TianmingLi/jetson-nano-baseboard/USB-3_2-HUB.kicad_sch

## KiCad design USB-3_2-HUB.kicad_sch (2023-06-30)

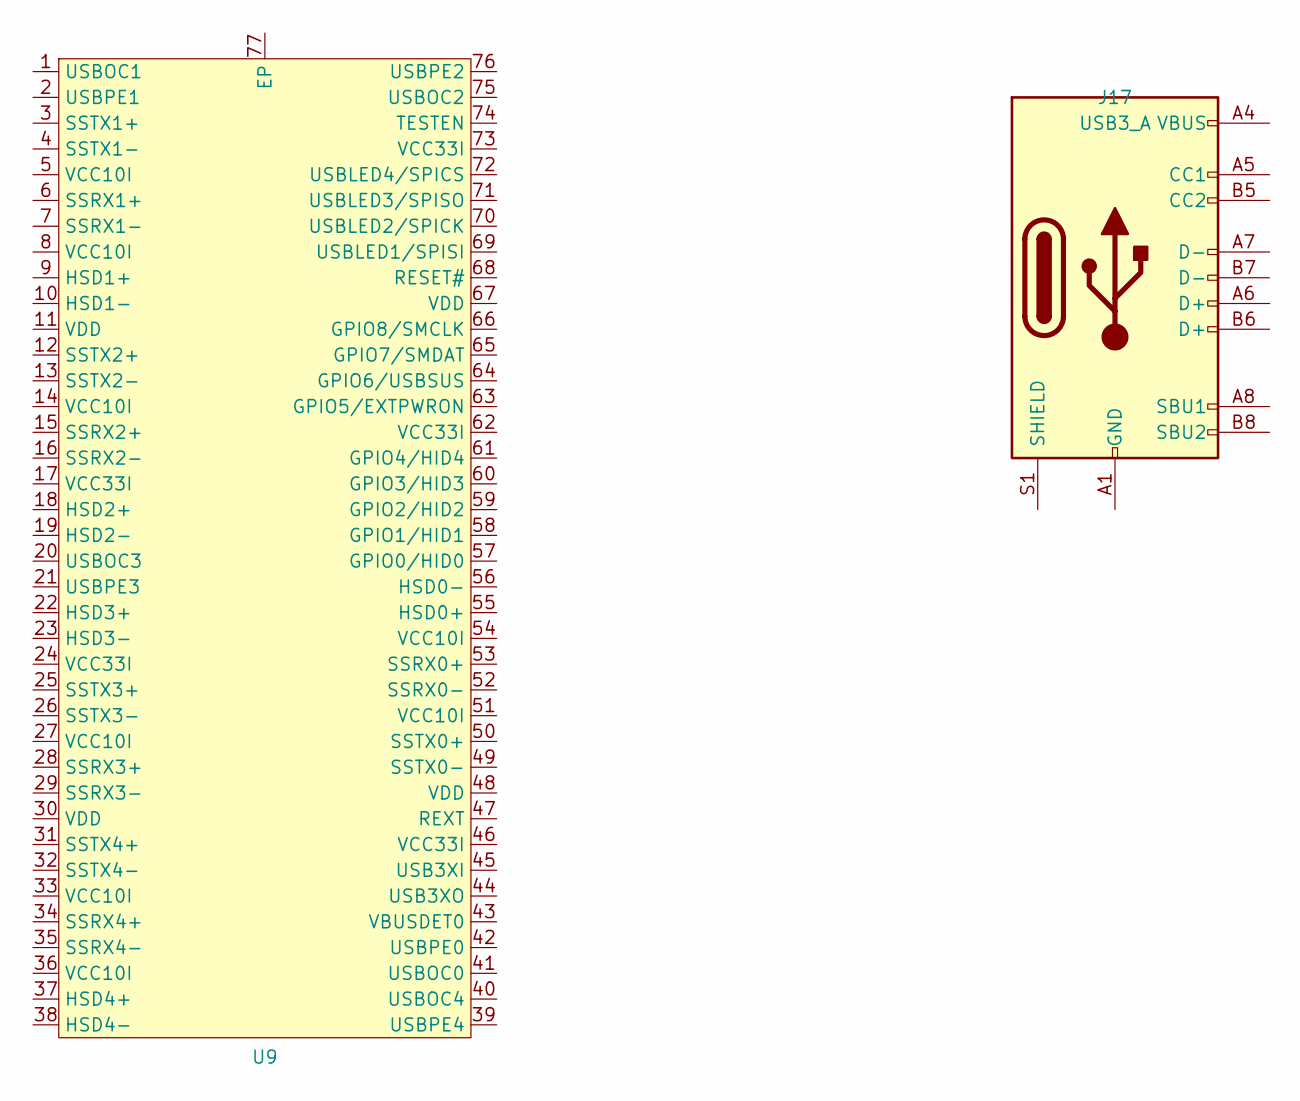
[picture p2: schematic USB-3_2-HUB.kicad_sch]

Parts:
J17: USB3_A; USB-A-TH_XUNPU_USB-303WSD-BRY
U9: QFN-76_L9.0-W9.0-P0.40-EP6.3-TL

Connections:
unnamed: J17.A1 (GND), J17.A12 (GND), J17.B1 (GND), J17.B12 (GND)
unnamed: J17.A4 (VBUS), J17.A9 (VBUS), J17.B4 (VBUS), J17.B9 (VBUS)
