TianmingLi/jetson-nano-baseboard/csi.kicad_sch

## KiCad design csi.kicad_sch (2023-06-30)

Schematic: csi.kicad_sch

Parts:
C9: C_100n_0402; 0402-cap; MPN 0402X104K6R3CT
J6: WE_68715014522; WE_68715014522_ONE-SIDE; MPN 68715014522
J7: WE_68715014022; MPN 68715014022
J15: Conn_01x15; FPC-SMD_AFA07-S15FCC-00
M1: jetson-nano-connector; PartSymbol 2309413-1
R13, R15, R17, R19, R21, R23, R57, R58, R59, R60, R61, R78, R79, R80: R_0R_0402; 0402-res; MPN ERJ2GE0R00X
R18, R22, R24, R25, R27, R28, R29, R33, R34, R35: R_2k_0402; 0402-res; MPN CRCW04022K00FKED
R69: R_100k_0402; 0402-res; MPN CRCW0402100KFKEDHP
R122: R_10k_0402; 0402-res; MPN CRCW040210K0FKEDHP
T8: BSS138APW; SC70-3; MPN BSS138PW
TP1, TP3, TP4, TP6, TP9, TP10: TP-R-1.5; MPN N/A
U4: PCA9547BS,118; HVQFN24; MPN PCA9547BS,118

Connections:
1V8_SYS: R23.2, R79.2
3V3_FFC1: J6.47, J6.48, J15.15, R78.2
3V3_FFC2: J7.47, J7.48, R80.2
3V3_SYS: C9.1, R34.1, R35.1, R122.1, U4.21 (VCC)
5V0_SYS: J6.49, J6.50, J7.49, J7.50
CAM0_SCL: J6.40, R15.1, R24.2
CAM0_SDA: J6.39, R13.1, R25.2
CAM1_MCLK: J15.12, M1.122 (CAM1_MCLK)
CAM1_PWDN: J15.11, M1.120 (CAM1_PWDN), TP6.1
CAM1_SCL: J6.42, R18.2, R21.1
CAM1_SDA: J6.41, R17.1, R22.2
CAM2_SCL: J7.42, R27.2, R58.1
CAM2_SDA: J7.41, R19.1, R28.2
CAM3_SCL: J7.40, R33.2, R61.1
CAM3_SDA: J7.39, R29.2, R59.1
CAM_I2C_SCL: J15.13, M1.213 (CAM_I2C_SCL), R35.2, R60.2, TP10.1
CAM_I2C_SDA: J15.14, M1.215 (CAM_I2C_SDA), R34.2, R57.2, TP1.1
CSI_A_CLK_N: J7.28, J15.9, M1.10 (CSI0_CLK_N)
CSI_A_CLK_P: J7.29, J15.8, M1.12 (CSI0_CLK_P)
CSI_A_D0_N: J7.25, J15.2, M1.4 (CSI0_D0_N)
CSI_A_D0_P: J7.26, J15.3, M1.6 (CSI0_D0_P)
CSI_A_D1_N: J7.23, J15.5, M1.16 (CSI0_D1_N)
CSI_A_D1_P: J7.24, J15.6, M1.18 (CSI0_D1_P)
CSI_B_D0_N: J7.21, M1.3 (CSI1_D0_N)
CSI_B_D0_P: J7.22, M1.5 (CSI1_D0_P)
CSI_B_D1_N: J7.19, M1.15 (CSI1_D1_N)
CSI_B_D1_P: J7.20, M1.17 (CSI1_D1_P)
CSI_C_CLK_N: J7.10, M1.52 (CSI4_CLK_N)
CSI_C_CLK_P: J7.11, M1.54 (CSI4_CLK_P)
CSI_C_D0_N: J7.7, M1.46 (CSI4_D0_N)
CSI_C_D0_P: J7.8, M1.48 (CSI4_D0_P)
CSI_C_D1_N: J7.5, M1.58 (CSI4_D1_N)
CSI_C_D1_P: J7.6, M1.60 (CSI4_D1_P)
CSI_D_D0_N: J7.3, M1.40 (CSI4_D2_N)
CSI_D_D0_P: J7.4, M1.42 (CSI4_D2_P)
CSI_D_D1_N: J7.1, M1.64 (CSI4_D3_N)
CSI_D_D1_P: J7.2, M1.66 (CSI4_D3_P)
CSI_E_CLK_N: J6.28, M1.28 (CSI2_CLK_N)
CSI_E_CLK_P: J6.29, M1.30 (CSI2_CLK_P)
CSI_E_D0_N: J6.25, M1.22 (CSI2_D0_N)
CSI_E_D0_P: J6.26, M1.24 (CSI2_D0_P)
CSI_E_D1_N: J6.23, M1.34 (CSI2_D1_N)
CSI_E_D1_P: J6.24, M1.36 (CSI2_D1_P)
CSI_F_CLK_N: M1.27 (CSI3_CLK_N)
CSI_F_CLK_P: M1.29 (CSI3_CLK_P)
CSI_F_D0_N: J6.21, M1.21 (CSI3_D0_N)
CSI_F_D0_P: J6.22, M1.23 (CSI3_D0_P)
CSI_F_D1_N: J6.19, M1.33 (CSI3_D1_N)
CSI_F_D1_P: J6.20, M1.35 (CSI3_D1_P)
CSI_G_CLK_N: J6.10, M1.76 (DSI_CLK_N)
CSI_G_CLK_P: J6.11, M1.78 (DSI_CLK_P)
CSI_G_D0_N: J6.7, M1.70 (DSI_D0_N)
CSI_G_D0_P: J6.8, M1.72 (DSI_D0_P)
CSI_G_D1_N: J6.5, M1.82 (DSI_D1_N)
CSI_G_D1_P: J6.6, M1.84 (DSI_D1_P)
GND: C9.2, J6.9, J6.12, J6.15, J6.18, J6.27, J6.30, J7.9, J7.12, J7.15, J7.18, J7.27, J7.30, J15.1, J15.4, J15.7, J15.10, R69.1, T8.2 (S), U4.9 (GND), U4.18 (A2), U4.22 (A0), U4.23 (A1), U4.25 (GND)
I2C_MUX_RESET: R69.2, T8.1 (G)
unnamed: M1.9 ((CSI1_CLK)RSVD), TP3.1
unnamed: M1.11 ((CSI1_CLK)RSVD), TP4.1
unnamed: M1.118 (GPIO01), TP9.1
unnamed: R13.2, U4.1 (SD0)
unnamed: R15.2, U4.2 (SC0)
unnamed: R17.2, U4.3 (SD1)
unnamed: R18.1, R22.1, R23.1, R24.1, R25.1, R78.1
unnamed: R19.2, U4.5 (SD2)
unnamed: R21.2, U4.4 (SC1)
unnamed: R27.1, R28.1, R29.1, R33.1, R79.1, R80.1
unnamed: R57.1, U4.20 (SDA)
unnamed: R58.2, U4.6 (SC2)
unnamed: R59.2, U4.7 (SD3)
unnamed: R60.1, U4.19 (SCL)
unnamed: R61.2, U4.8 (SC3)
unnamed: R122.2, T8.3 (D), U4.24 (~RESET)
VSYNC_CAM1_1: J6.32
VSYNC_CAM1_2: J6.34
VSYNC_CAM2_1: J7.32, M1.114 (CAM0_PWDN)
VSYNC_CAM2_2: J7.34

Notes on the sheet:
RIGHT CAMERA
CAM_R_CLK_N
CAM_R_SCL
CAM_R_D1_P
CAM_R_D0_P
CAM_L_SCL
CAM_L_D1_P
Text
CAM_L_D3_P
CAM_L_SDA
CAM_L_D0_P
LEFT CAMERA
CAM_L_CLK_N
CAM_R_CLK_P
CAM_L_D1_N
CAM_R_D3_P
CAM_R_D3_N
Camera FFC Rasperberrypi Cam #1
CAM_L_D2_N
Camera FFC #2
SoM interface
CAM_R_D0_N
CAM_L_CLK_P
CAM_R_D2_P
CAM_R_D2_N
Camera Interfaces
CAM_L_D3_N
CAM_L_D2_P
Camera FFC #1
Camera I2C multiplexer
CAM_R_SDA
CAM_R_D1_N
CAM_L_D0_N
