TianmingLi/jetson-nano-baseboard/display.kicad_sch

## KiCad design display.kicad_sch (2023-06-30)

Schematic: display.kicad_sch

Parts:
C1, C2, C3, C4: C_4u7_0402; 0402-cap; MPN GRM155R61A475MEAAD
C5, C6, C7, C8, C12, C26, C27, C39, C40, C42, C43, C44, C45, C73, C74, C75, C76, C77, C78, C79, C80: C_100n_0402; 0402-cap; MPN 0402X104K6R3CT
D2, D4: 1N4148WS; SOD-323; MPN 1N4148WS
D10, D11, D12: PESD2USB5UV-TR; SOT-23s; MPN PESD2USB5UV-TR
IC2, IC18: SON-15; PartSymbol TPD8S009DSMR
IC6: PCA9517ADP; MSOP-8; MPN PCA9517ADP
IC11: SN74LV1T125DBVR; SOT-23-5; MPN SN74LV1T125DBVR
J1: 46756-1001; HDMI-SMD_HDMI-001C; MPN c2836126
J2: 2129320-3; DP-SMD_HYC16-DP20-178; MPN 2309413-1
L8, L9, L10: BLM18SG121TN1D; 0603; MPN BLM18SG121TN1D
M1: jetson-nano-connector; PartSymbol 2309413-1
R1, R2, R3, R4, R7, R8, R9, R10: R_5R6_0402; 0402-res; MPN ERJ2GEJ5R6X
R5, R6, R11, R37, R81, R83, R88: R_2k_0402; 0402-res; MPN CRCW04022K00FKED
R12, R82, R98, R99: R_0R_0402; 0402-res; MPN ERJ2GE0R00X
R26, R30, R100: R_100k_0402; 0402-res; MPN CRCW0402100KFKEDHP
R31, R32: R_1M0_0402; 0402-res; MPN CRG0402F1M0
T1: BSS138APW; SC70-3; MPN BSS138PW
TP2, TP25, TP26, TP33, TP34, TP35, TP36: TP-R-1.5; MPN N/A

Connections:
1V8_SYS: C5.1, IC11.5 (VCC), R88.1
3V3_SYS: C26.1, IC6.1 (VCCA), L10.1, R11.1, R81.1
5V0_SYS: IC2.13 (VCC), IC2.15 (VCC), L9.1
DP_CEC: J2.6 (CONFIG2), R32.2
DP_HPD: IC11.4 (Y), M1.88 (DP0_HPD)
DP_HPD_IN: D12.2 (IO2), IC11.2 (A), J2.2 (HOTPLUG), R100.2
DP_MODE: J2.4 (CONFIG1), R31.2
DP_PWR: D2.A, L10.2, R26.2
EDP0_TX_N: C40.1, M1.39 (DP0_TXD0_N)
EDP0_TX_P: C39.1, M1.41 (DP0_TXD0_P)
EDP1_TX_N: C43.1, M1.45 (DP0_TXD1_N)
EDP1_TX_P: C42.1, M1.47 (DP0_TXD1_P)
EDP2_TX_N: C7.1, M1.51 (DP0_TXD2_N)
EDP2_TX_P: C6.1, M1.53 (DP0_TXD2_P)
EDP3_TX_N: C12.1, M1.57 (DP0_TXD3_N)
EDP3_TX_P: C8.1, M1.59 (DP0_TXD3_P)
EDP_AUX_N: C45.1, M1.90 (DP0_AUX_N)
EDP_AUX_P: C44.1, M1.92 (DP0_AUX_P)
EDP_C_AUX_C_N: C45.2, J2.18 (AUX_CH_N), R26.1
EDP_C_AUX_C_P: C44.2, J2.16 (AUX_CH_P), R30.2
GND: C1.1, C2.1, C3.1, C4.1, C5.2, C26.2, C27.1, D10.3 (GND), D11.3 (GND), D12.3 (GND), IC2.2 (GND), IC2.5 (GND), IC2.8 (GND), IC2.11 (GND), IC6.4 (GND), IC11.1 (~OE), IC11.3 (GND), IC18.2 (GND), IC18.5 (GND), IC18.8 (GND), IC18.11 (GND), J2.1 (GND), J2.7 (GND), J2.8 (GND), J2.13 (GND), J2.14 (GND), J2.19 (GND), J2.21 (SHIELD), J2.22 (SHIELD), J2.23 (SHIELD), J2.24 (SHIELD), L8.1, R12.1, R30.1, R31.1, R32.1, R37.2, R83.2, R100.1, T1.2 (S)
HDMI_PWR: C27.2, D4.A, IC6.5 (EN), IC6.8 (VCCB), IC18.13 (VCC), IC18.15 (VCC), L9.2, R5.1, R6.1
HDMI_SHIELD: J1.4 (D2S), J1.7 (D1S), J1.10 (D0S), J1.13 (CKS), J1.SH, L8.2
M2_ALERT: M1.212 (GPIO10), TP2.1
ML_C_LANE0_N: C40.2, IC2.3 (D0-), J2.5 (ML_LANE0_N)
ML_C_LANE0_P: C39.2, IC2.1 (D0+), J2.3 (ML_LANE0_P)
ML_C_LANE1_N: C43.2, IC2.6 (D1-), J2.11 (ML_LANE1_N)
ML_C_LANE1_P: C42.2, IC2.4 (D1+), J2.9 (ML_LANE1_P)
ML_C_LANE2_N: C7.2, IC2.9 (D2-), J2.17 (ML_LANE2_N)
ML_C_LANE2_P: C6.2, IC2.7 (D2+), J2.15 (ML_LANE2_P)
ML_C_LANE3_N: C12.2, IC2.12 (D3-), J2.12 (ML_LANE3_N)
ML_C_LANE3_P: C8.2, IC2.10 (D3+), J2.10 (ML_LANE3_P)
unnamed: C1.2, C2.2, D4.C, J1.19 (+5V)
unnamed: C3.2, C4.2, D2.C, J2.20 (DP_PWR)
unnamed: IC6.2 (SCLA), R81.2, R98.1
unnamed: IC6.3 (SDAA), R11.2, R99.1
unnamed: J1.16 (GND), R12.2
unnamed: R82.2, R83.1, T1.1 (G)
TMDS_C1_CLK_N: C80.2, IC18.12 (D3-), R10.1
TMDS_C1_CLK_P: C78.2, IC18.10 (D3+), R9.1
TMDS_C1_D0_N: C79.2, IC18.9 (D2-), R8.1
TMDS_C1_D0_P: C76.2, IC18.7 (D2+), R7.1
TMDS_C1_D1_N: C77.2, IC18.6 (D1-), R4.1
TMDS_C1_D1_P: C75.2, IC18.4 (D1+), R3.1
TMDS_C1_D2_N: C74.2, IC18.3 (D0-), R2.1
TMDS_C1_D2_P: C73.2, IC18.1 (D0+), R1.1
TMDS_CEC: M1.94 (HDMI_CEC), TP26.1
TMDS_CEC_IN: D11.2 (IO2), J1.15 (CEC), R37.1
TMDS_CLK_C_N: J1.14 (CK-), R10.2
TMDS_CLK_C_P: J1.12 (CK+), R9.2
TMDS_CLK_N: C80.1, M1.81 (DP1_TXD3_N)
TMDS_CLK_P: C78.1, M1.83 (DP1_TXD3_P)
TMDS_D0_C_N: J1.11 (D0-), R8.2
TMDS_D0_C_P: J1.9 (D0+), R7.2
TMDS_D0_N: C79.1, M1.75 (DP1_TXD2_N)
TMDS_D0_P: C76.1, M1.77 (DP1_TXD2_P)
TMDS_D1_C_N: J1.8 (D1-), R4.2
TMDS_D1_C_P: J1.6 (D1+), R3.2
TMDS_D1_N: C77.1, M1.69 (DP1_TXD1_N)
TMDS_D1_P: C75.1, M1.71 (DP1_TXD1_P)
TMDS_D2_C_N: J1.5 (D2-), R2.2
TMDS_D2_C_P: J1.3 (D2+), R1.2
TMDS_D2_N: C74.1, M1.63 (DP1_TXD0_N)
TMDS_D2_P: C73.1, M1.65 (DP1_TXD0_P)
TMDS_HPD: M1.96 (DP1_HPD), R88.2, T1.3 (D), TP25.1
TMDS_HPD_IN: D11.1 (IO1), J1.1 (HPD/HEAC-), R82.1
TMDS_SCL: M1.100 (DP1_AUX_P), R98.2, TP33.1
TMDS_SCL_5V0: D10.1 (IO1), IC6.7 (SCLB), J1.17 (SCL), R5.2
TMDS_SDA: M1.98 (DP1_AUX_N), R99.2, TP34.1
TMDS_SDA_5V0: D10.2 (IO2), IC6.6 (SDAB), J1.18 (SDA), R6.2
USR_BUTTON: M1.218 (GPIO12), TP36.1
USR_LED: M1.206 (GPIO07), TP35.1
~OTG_USB_VBUS_DET: M1.87 (GPIO00)

Notes on the sheet:
5V0
DDC/HPD
3V3
HDMI Interface
DisplayPort Interface
1V8
Text
Display
