TianmingLi/jetson-nano-baseboard/interfaces.kicad_sch

## KiCad design interfaces.kicad_sch (2023-06-30)

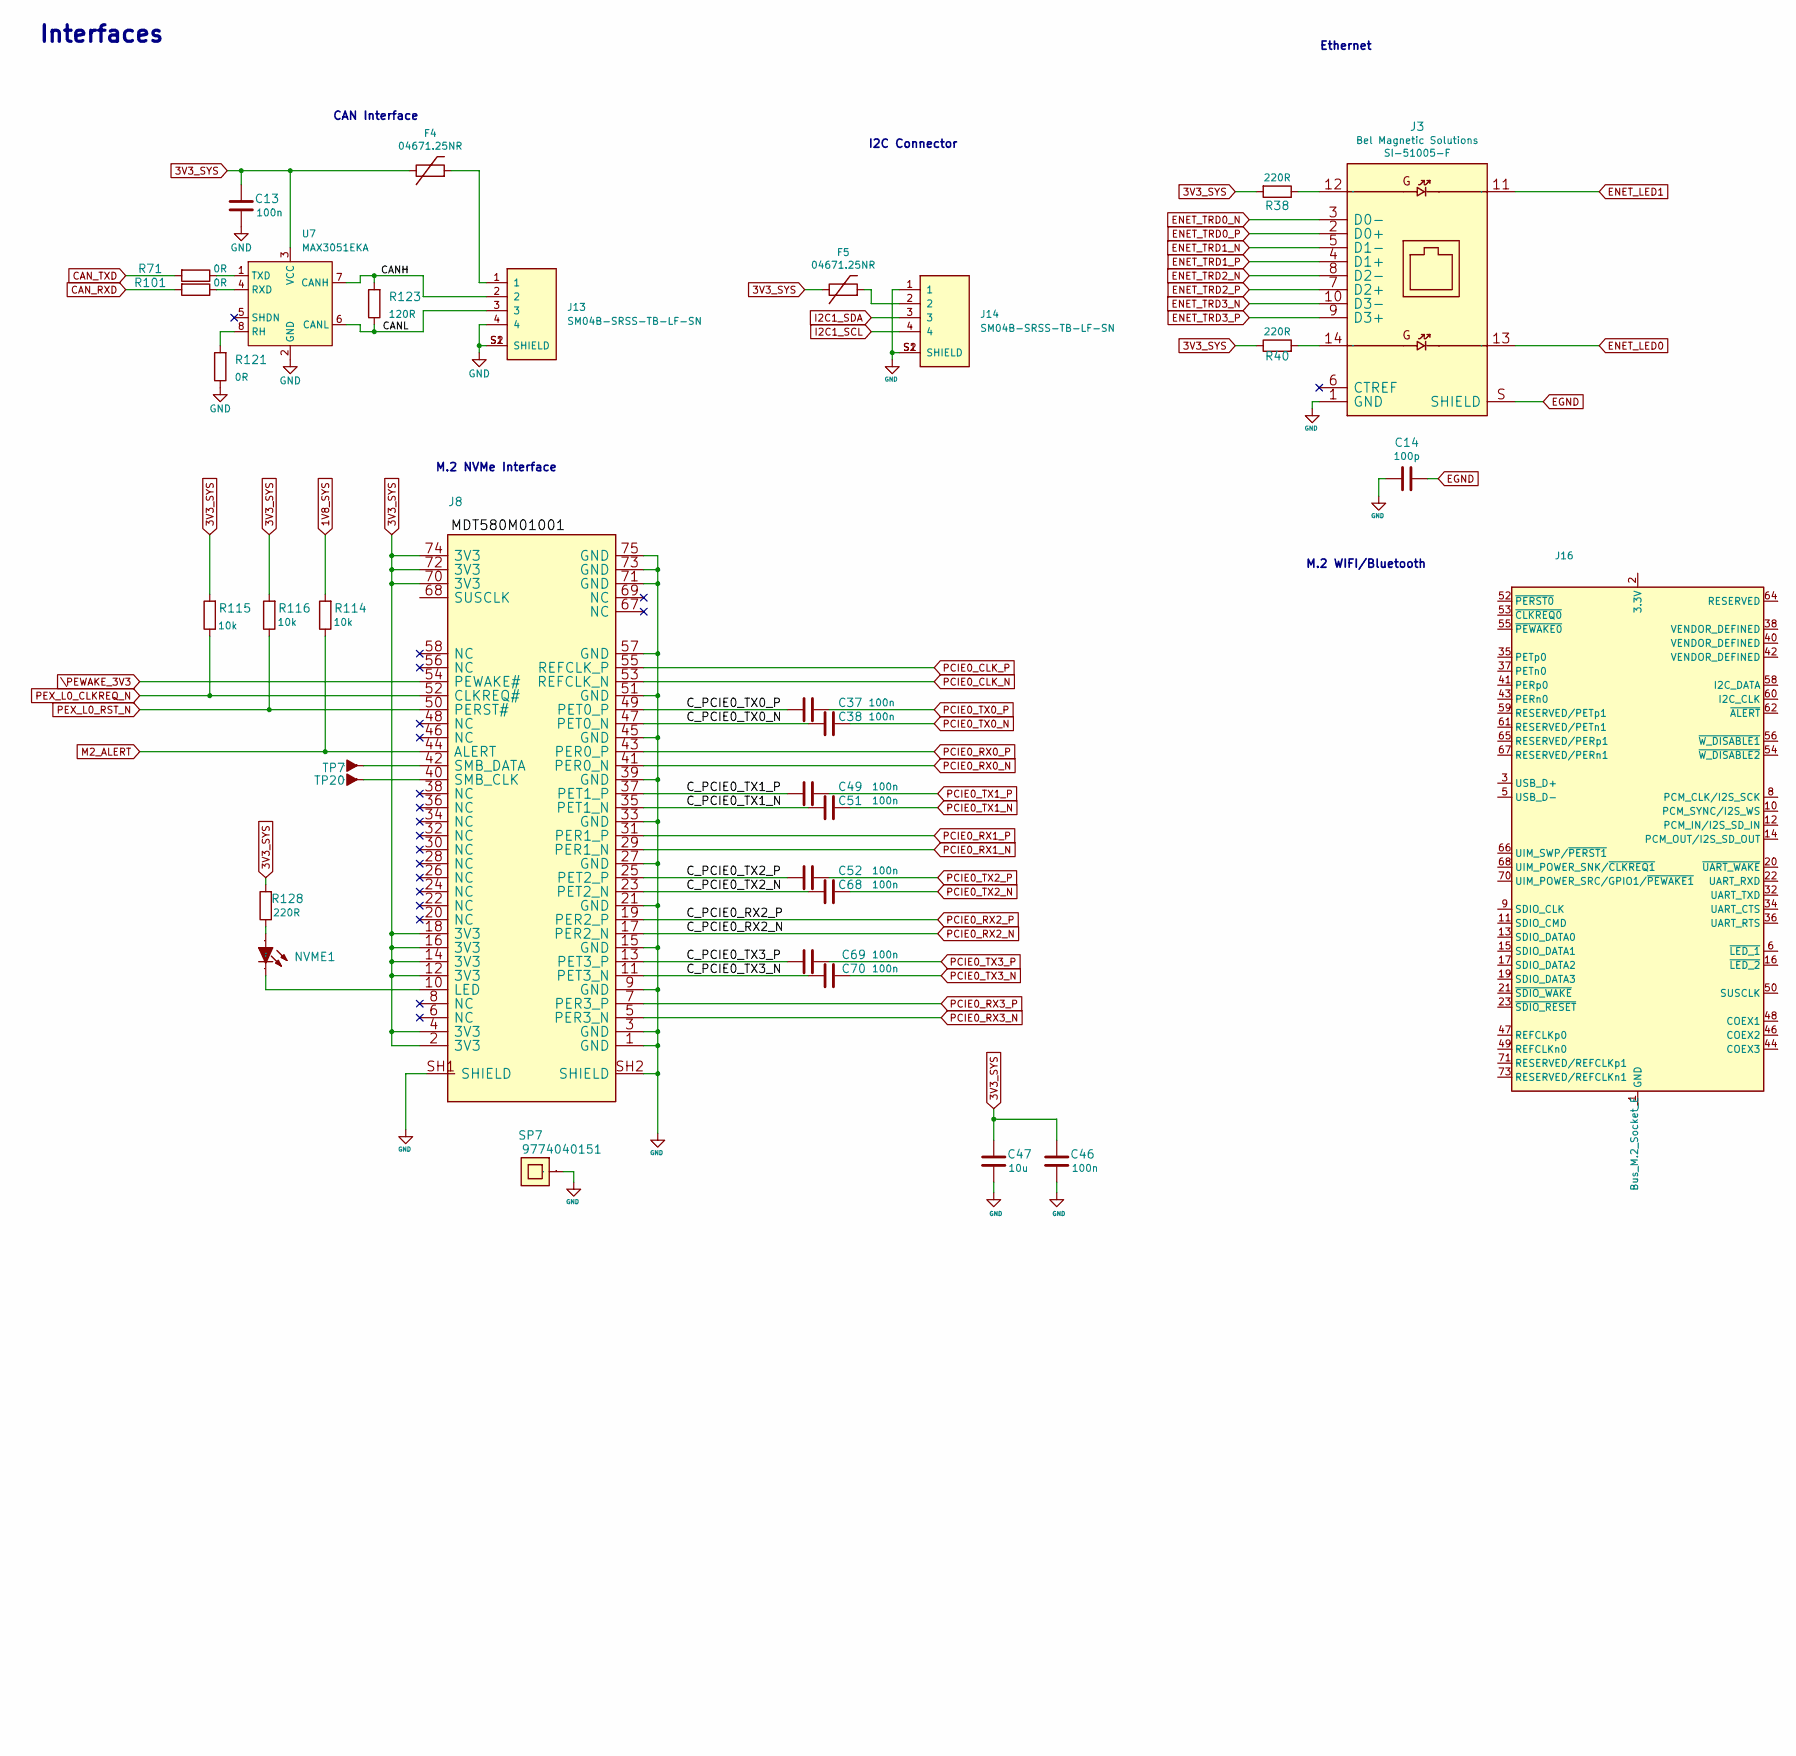
[picture p3: schematic interfaces.kicad_sch, part in row 1, column 1]

Parts:
C13, C37, C38, C46, C49, C51, C52, C68, C69, C70: C_100n_0402; 0402-cap; MPN 0402X104K6R3CT
C14: C_100p_0402; 0402-cap; MPN 0402N101J500CT
C47: C_10u_0603; 0603-cap; MPN GRM188R61A106KE69D
F4, F5: 04671.25NR; 0603-Fuse-Littelfuse-0467; MPN 04671.25NR
J3: SI-51005-F; MPN SI-51005-F
J8: MDT580M01001; MPN MDT580M01001
J13, J14: SM04B-SRSS-TB-LF-SN; MPN SM04B-SRSS-TB-LF-SN
J16: Bus_M.2_Socket_E; CONN-SMD_APCI0108-P001A
NVME1: LED0603; MPN KPT-1608SGC
R38, R40, R128: R_220R_0402; 0402-res; MPN ERJ2GEJ221X
R71, R101, R121: R_0R_0402; 0402-res; MPN ERJ2GE0R00X
R114, R115, R116: R_10k_0402; 0402-res; MPN CRCW040210K0FKEDHP
R123: R_120R_0402; 0402-res; MPN ERJ2GEJ121X
SP7: 9774040151; 9774060151; MPN 9774040151
TP7, TP20: TP-R-1.5; MPN N/A
U7: MAX3051EKA; SOT-23-8; MPN MAX3051EKA

Connections:
1V8_SYS: R114.2
3V3_SYS: C13.2, C46.2, C47.2, F4.1, F5.1, J8.2 (3V3), J8.4 (3V3), J8.12 (3V3), J8.14 (3V3), J8.16 (3V3), J8.18 (3V3), J8.70 (3V3), J8.72 (3V3), J8.74 (3V3), R38.2, R40.1, R115.2, R116.2, R128.2, U7.3 (VCC)
CANH: J13.2, R123.2, U7.7 (CANH)
CANL: J13.3, R123.1, U7.6 (CANL)
CAN_RXD: R101.2
CAN_TXD: R71.2
C_PCIE0_TX0_N: C38.1, J8.47 (PET0_N)
C_PCIE0_TX0_P: C37.1, J8.49 (PET0_P)
C_PCIE0_TX1_N: C51.1, J8.35 (PET1_N)
C_PCIE0_TX1_P: C49.1, J8.37 (PET1_P)
C_PCIE0_TX2_N: C68.1, J8.23 (PET2_N)
C_PCIE0_TX2_P: C52.1, J8.25 (PET2_P)
C_PCIE0_TX3_N: C70.1, J8.11 (PET3_N)
C_PCIE0_TX3_P: C69.1, J8.13 (PET3_P)
EGND: C14.1, J3.S (SHIELD)
ENET_LED0: J3.13
ENET_LED1: J3.11
ENET_TRD0_N: J3.3 (D0-)
ENET_TRD0_P: J3.2 (D0+)
ENET_TRD1_N: J3.5 (D1-)
ENET_TRD1_P: J3.4 (D1+)
ENET_TRD2_N: J3.8 (D2-)
ENET_TRD2_P: J3.7 (D2+)
ENET_TRD3_N: J3.10 (D3-)
ENET_TRD3_P: J3.9 (D3+)
GND: C13.1, C14.2, C46.1, C47.1, J3.1 (GND), J8.1 (GND), J8.3 (GND), J8.9 (GND), J8.15 (GND), J8.21 (GND), J8.27 (GND), J8.33 (GND), J8.39 (GND), J8.45 (GND), J8.51 (GND), J8.57 (GND), J8.71 (GND), J8.73 (GND), J8.75 (GND), J8.SH1 (SHIELD), J8.SH2 (SHIELD), J13.4, J13.S1 (SHIELD), J13.S2 (SHIELD), J14.1, J14.S1 (SHIELD), J14.S2 (SHIELD), R121.1, SP7.1, U7.2 (GND)
I2C1_SCL: J14.4
I2C1_SDA: J14.3
M2_ALERT: J8.44 (ALERT), R114.1
unnamed: F4.2, J13.1
unnamed: F5.2, J14.2
unnamed: J3.12, R38.1
unnamed: J3.14, R40.2
unnamed: J8.10 (LED), NVME1.2 (K)
unnamed: J8.40 (SMB_CLK), TP20.1
unnamed: J8.42 (SMB_DATA), TP7.1
unnamed: J16.1 (GND), J16.7 (GND), J16.18 (GND), J16.33 (GND), J16.39 (GND), J16.45 (GND), J16.51 (GND), J16.57 (GND), J16.63 (GND), J16.69 (GND), J16.75 (GND)
unnamed: J16.2 (3.3V), J16.4 (3.3V), J16.72 (3.3V), J16.74 (3.3V)
unnamed: NVME1.1 (A), R128.1
unnamed: R71.1, U7.1 (TXD)
unnamed: R101.1, U7.4 (RXD)
unnamed: R121.2, U7.8 (RH)
PCIE0_CLK_N: J8.53 (REFCLK_N)
PCIE0_CLK_P: J8.55 (REFCLK_P)
PCIE0_RX0_N: J8.41 (PER0_N)
PCIE0_RX0_P: J8.43 (PER0_P)
PCIE0_RX1_N: J8.29 (PER1_N)
PCIE0_RX1_P: J8.31 (PER1_P)
PCIE0_RX2_N: J8.17 (PER2_N)
PCIE0_RX2_P: J8.19 (PER2_P)
PCIE0_RX3_N: J8.5 (PER3_N)
PCIE0_RX3_P: J8.7 (PER3_P)
PCIE0_TX0_N: C38.2
PCIE0_TX0_P: C37.2
PCIE0_TX1_N: C51.2
PCIE0_TX1_P: C49.2
PCIE0_TX2_N: C68.2
PCIE0_TX2_P: C52.2
PCIE0_TX3_N: C70.2
PCIE0_TX3_P: C69.2
PEX_L0_CLKREQ_N: J8.52 (CLKREQ#), R115.1
PEX_L0_RST_N: J8.50 (PERST#), R116.1
\PEWAKE_3V3: J8.54 (PEWAKE#)

Notes on the sheet:
Text
I2C Connector
CAN Interface
M.2 NVMe Interface
M.2 WIFI/Bluetooth
Interfaces
Ethernet
