TianmingLi/jetson-nano-baseboard/jetson-nano-baseboard.kicad_sch

## KiCad design jetson-nano-baseboard.kicad_sch (2023-06-30)

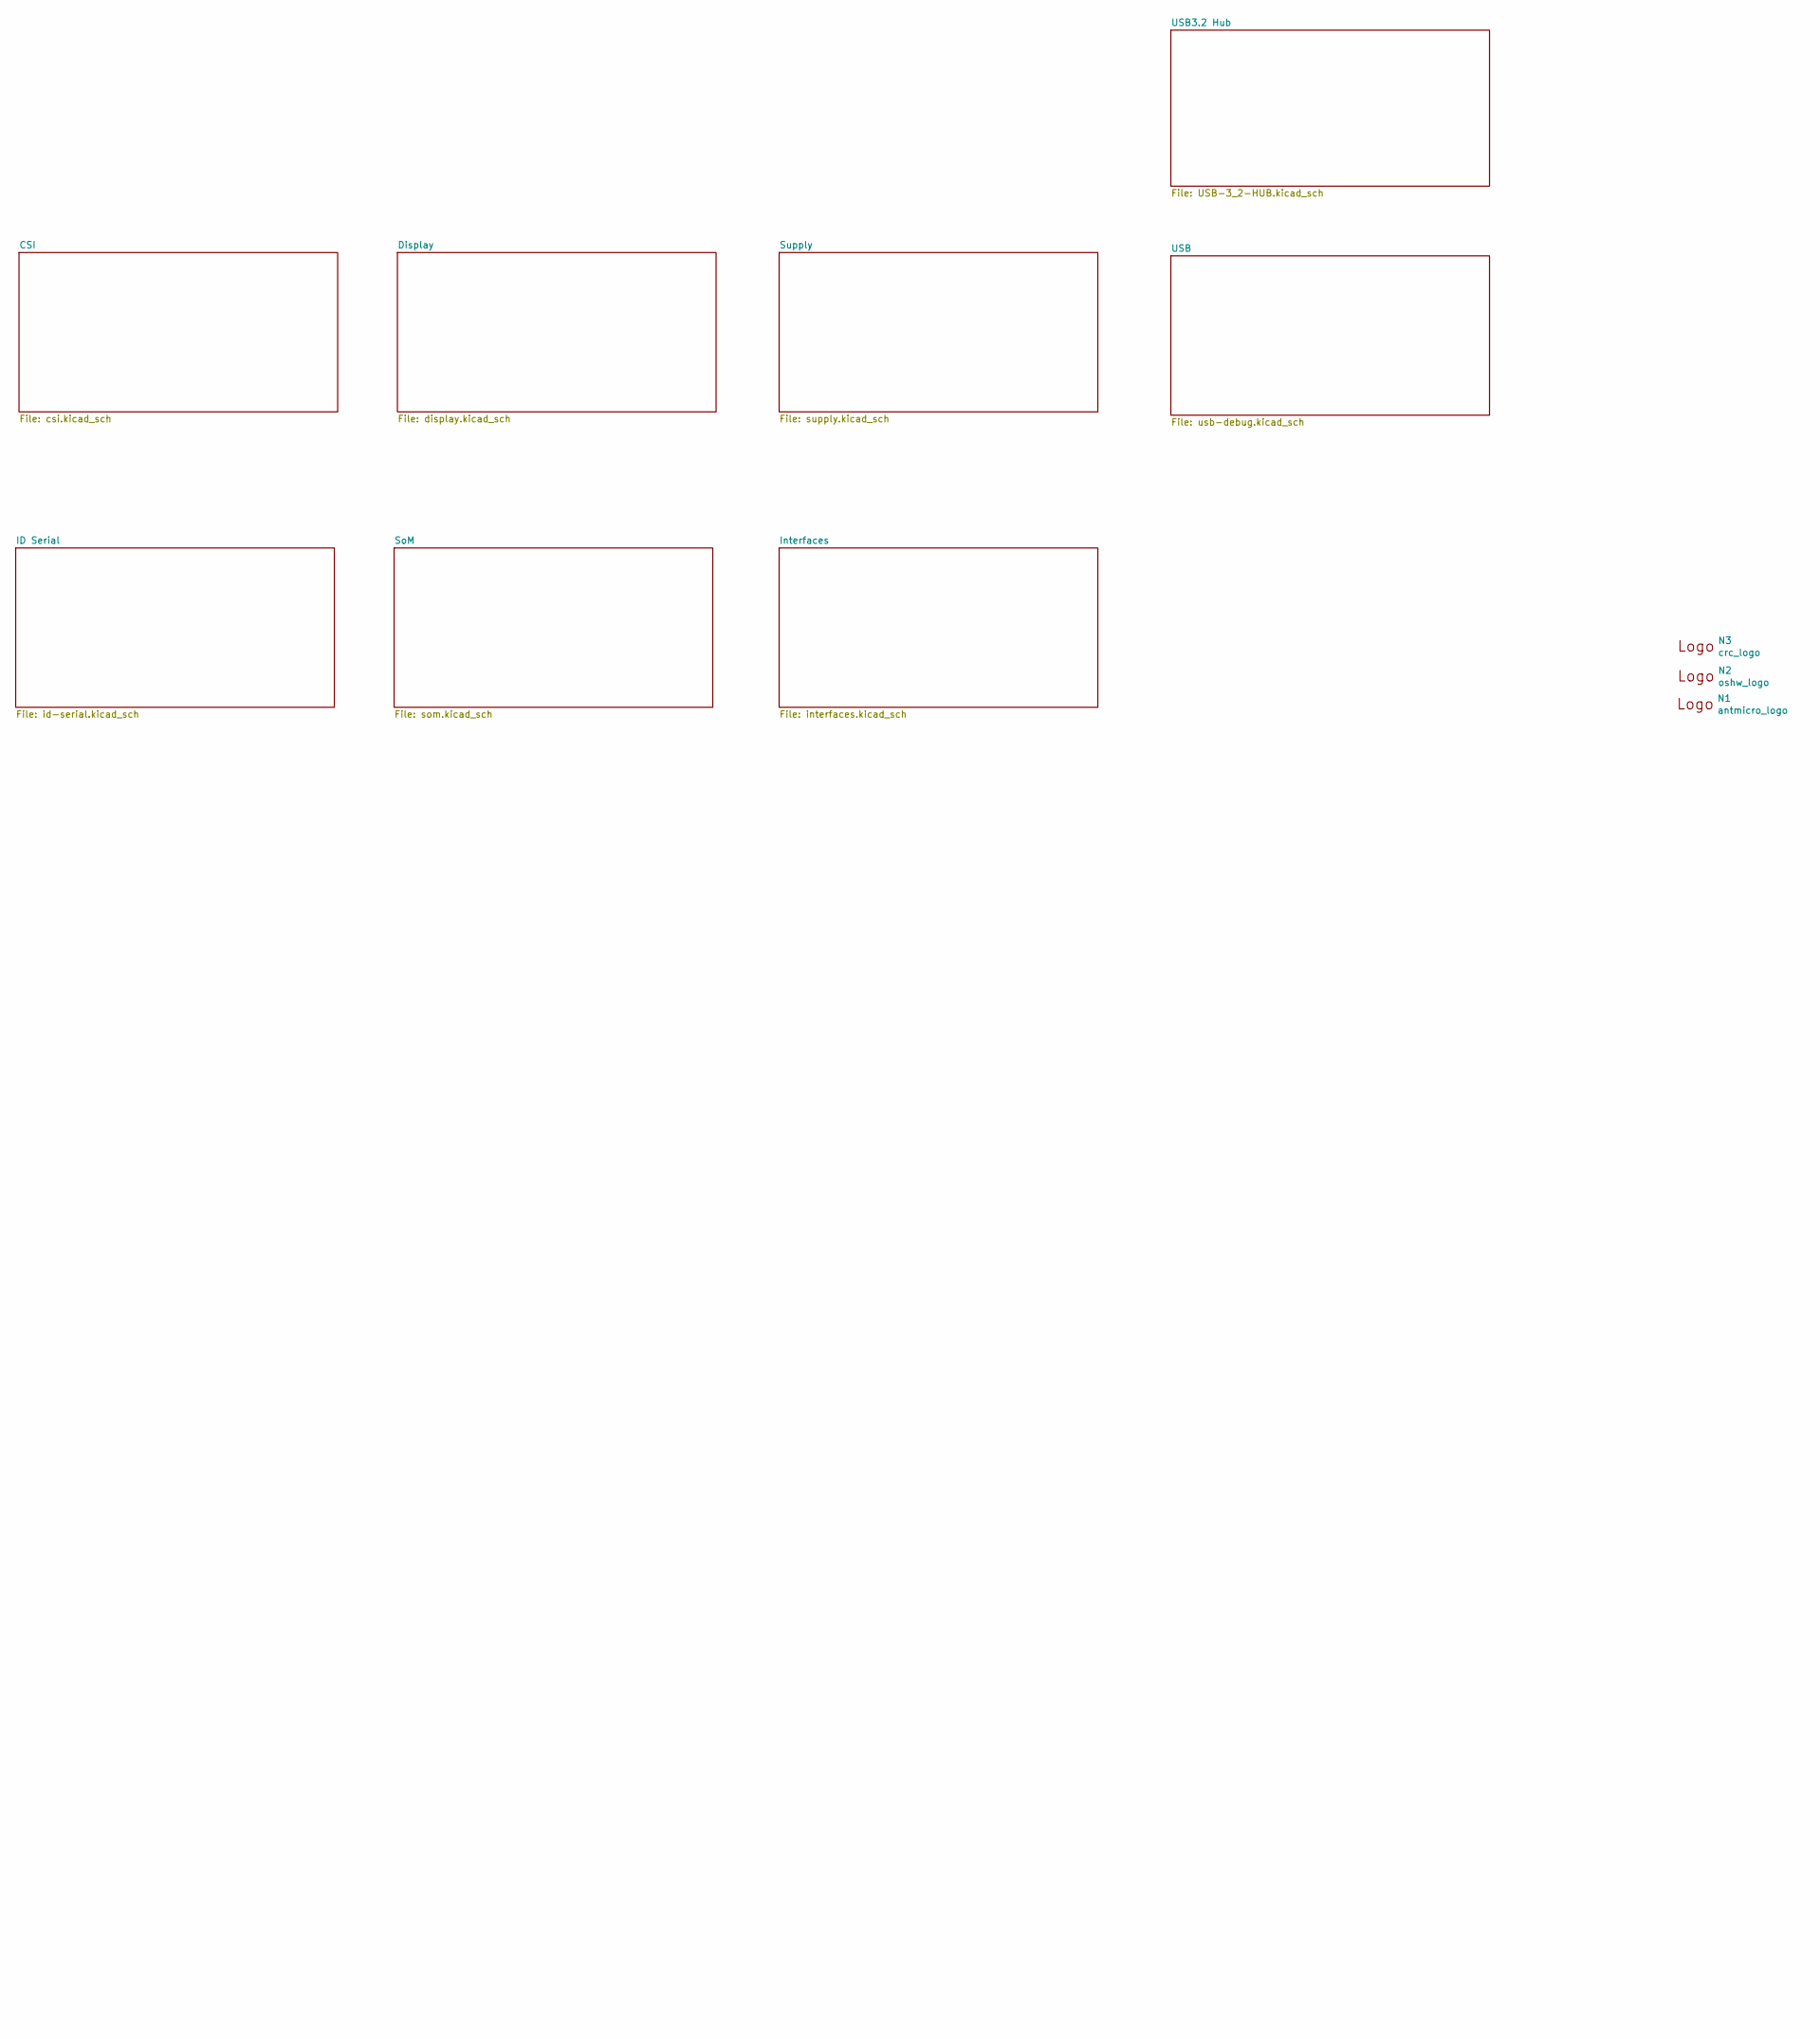
[picture p4: schematic jetson-nano-baseboard.kicad_sch, part in row 1, column 1]

Parts:
N1: antmicro_logo; antmicro-logo_scaled_15mm
N2: oshw_logo; oshw-logo
N3: crc_logo; CRC_logo_15mm

Notes on the sheet:
Text
