TianmingLi/jetson-nano-baseboard/supply.kicad_sch

## KiCad design supply.kicad_sch (2023-06-30)

Schematic: supply.kicad_sch

Parts:
C16, C18, C60: C_2u2_0402; 0402-cap; MPN C1005X5R1A225K050BC
C17, C19, C21, C22: C_10u_1206_50V; 1206-cap; MPN C3216X7R1H106K160AE
C20, C59, C64: C_47u_0805; 0805-cap; MPN C0805C476M9PACTU
C23, C55, C63, C81: C_10u_0603; 0603-cap; MPN GRM188R61A106KE69D
C24: C_6p_0402; 0402-cap; MPN 0402N6R0D500CT
C25: C_10u_0805; 0805-cap; MPN 160R15X106KV4E
C28: C_270p_25V_0402; 0402-res; MPN C0402C271J3GAC7867
C41: C_47n_0402; 0402-cap; MPN MC0402X473K160CT
C56: C_100n_0402_50V; 0402-cap; MPN GRM155R71H104KE14D
C57, C71, C83, C86, C88, C89: C_100n_0402; 0402-cap; MPN 0402X104K6R3CT
C58: C_33n_0402; 0402-cap; MPN MC0402B333K250CT
C61, C82: C_1n2_50V_0402; 0402-res; MPN GCM155R71H122KA37D
C65, C84, C87: C_1u_0402; 0402-cap; MPN C1005X6S1A105K050BC
C85: C_4u7_0603; 0603-cap; MPN C1608X5R1V475M080AC
D1, D9: ESD5B5_0ST1G; SOD-523_NP; MPN ESD5B5.0ST1G
D13: 1N4148WS; SOD-323; MPN 1N4148WS
D14: SMBJ33A; D_SMB; MPN SMBJ33A
F1, F2: 04671.25NR; 0603-Fuse-Littelfuse-0467; MPN 04671.25NR
F3: 3413_0329_22; 1206; MPN 3413.0329.22
FB1: 74279221100; 1206-res; MPN 74279221100
FB3: 74279220181; 0805-res; MPN 74279220181
IC4: TPS7A0518PDBVT; SOT-23-5; MPN TPS7A0518PDBVT
IC12: 74HC00PW; TSSOP-14; MPN 74HC00PW
IC13: SN74LVC1G126DCKR; R-PDSO-G5; MPN SN74LVC1G126DCKR
J4: CONN-TH_XT30PW-M; MPN MJ-179PH
J12: 533980471; Molex_PicoBlade_53398-0471_1x04-1MP_P1.25mm_Vertical; MPN 0533980471
L1: XFL4020-222MEC; XFL4015-122MEC; MPN XFL4020-222MEC
L4: IHLP3232DZER3R3M01; IHLP3232DZ; MPN IHLP3232DZER3R3M01
L5, L6: LQH32PN2R2NN0L; MPN LQH32PN2R2NN0L
R16, R36, R45, R87: R_1k_0402; 0402-res; MPN CR0402-FX-1001GLF
R39, R44, R46, R52, R95, R120: R_10k_0402; 0402-res; MPN CRCW040210K0FKEDHP
R48, R76, R92, R93, R130: R_0R_0402; 0402-res; MPN ERJ2GE0R00X
R70: R_100R_0402; 0402-res; MPN CR0402-FX-1000GLF
R74: R_2k_0402; 0402-res; MPN CRCW04022K00FKED
R75: R_316k_0402; 0402-res; MPN CRCW0402316KFKED
R77: R_60k4_1%_0402; 0402-res; MPN ERJ-2RKF6042X
R84, R86: R_200k_0402; 0402-res; MPN RC0402FR-07200KL
R85: R_470k_0402; 0402-res; MPN RC0402FR-07470KL
R89: R_3R3_0402; 0402-res; MPN ERJ2GEJ3R3X
R90: R_26k7_0402; 0402-res; MPN MCMR04X2672FTL
R91, R96: R_100k_0402; 0402-res; MPN CRCW0402100KFKEDHP
R94: R_8k66_1%_0402; 0402-res; MPN RC0402FR-078K66L
R117: R_52k3_0402; 0402-res; MPN ERJ-2RKF5232X
R118: R_100k_1%_0402; 0402; MPN ERA-6AEB104V
R119: R_44k2_0402; 0402-res; MPN ERJ2RKF4422X
T3: BSS138APW; SC70-3; MPN BSS138PW
TP5, TP8, TP16, TP17, TP42, TP44, TP47: TP-R-1.5; MPN N/A
TP11, TP12, TP15, TP40, TP41: Testpad; TP-R-1.5; MPN N/A
U1, U5: LM3671MF-3.3/NOPB; SOT-23-5; MPN LM3671MF-3.3/NOPB
U2: LM62440-Q1; VQFN-14-HR; MPN LMQ62440BPPQRJRRQ1
U3: SN74LXC1T45DBVR; SOT-23-6; MPN SN74LXC1T45DBVR
U6: SIC477ED-T1-GE3; SIC47XED-T1-GE3; MPN SIC477ED-T1-GE3

Connections:
1V8_SYS: C65.1, C86.2, IC4.5 (VOUT), R95.1, T3.1 (G), TP47.1, U3.1 (VCCA), U3.5 (DIR)
3V3_EN: R44.1, U2.7 (EN)
3V3_FB: R45.2, R48.2, R118.2, R119.1, U2.4 (FB)
3V3_FFC1: F1.2
3V3_FFC2: F2.1
3V3_R_C_BOOT: C89.2, R70.2, U2.14 (CBOOT)
3V3_SW: C89.1, L1.2, U2.10 (SW)
3V3_SYS: C20.1, C24.1, C25.1, D1.2, L1.1, R48.1, R118.1, U2.1 (BIAS)
3V3_VCC: C87.1, U2.2 (VCC)
3V3_VIN: C19.1, C21.1, FB3.2, U2.8 (VIN1), U2.12 (VIN2)
5V0_SYS: C16.1, C18.1, C59.1, C60.1, C64.1, C71.2, C81.1, C82.1, C83.2, C88.2, D9.2, IC4.1 (VIN), IC12.14 (VCC), IC13.1 (OE), IC13.5 (VCC), J12.2, L4.2, R16.1, R36.1, R46.2, R84.2, R86.2, R93.1, R117.1, TP41.1, TP42.1, U1.1 (Vin), U3.6 (VCCB), U5.1 (Vin)
5V_BOOT: C57.1, U6.4 (BOOT)
5V_COMP: R75.1, U6.21 (NC)
5V_EN: R91.1, TP15.1, U6.3 (EN)
5V_FB: R117.2, R120.1, U6.22 (VFB)
5V_FSW: R90.1, U6.24 (FSW)
5V_ILIM: R76.1, R77.1, U6.25 (ILIMIT)
5V_MODE: R74.1, U6.27 (MODE)
5V_PHASE: R89.2, U6.5 (PHASE), U6.6 (PHASE)
5V_SNS: C61.1, C82.2, R94.2
5V_SS: C58.1, U6.19 (SS)
5V_SW: L4.1, R94.1, U6.12 (SW), U6.13 (SW), U6.14 (SW)
5V_VIN: C17.1, C22.1, C56.1, FB1.2, R91.2, TP11.1, U6.1 (VCIN), U6.7 (VIN), U6.8 (VIN)
#RESET: R39.2, R44.2, R52.2, R92.2
#SHUTDOWN_REQ: IC12.4 (2A), R86.1
FAN_PMW_5V: J12.4, U3.4 (B)
FAN_PWM: U3.3 (A)
FAN_TACH: R95.2, T3.2 (S)
FAN_TACH_5V: J12.3, R46.1, T3.3 (D)
GND: C16.2, C17.2, C18.2, C19.2, C20.2, C21.2, C22.2, C23.2, C25.2, C28.1, C41.1, C55.2, C56.2, C58.2, C59.2, C60.2, C63.1, C64.2, C65.2, C71.1, C81.2, C83.1, C84.2, C85.2, C86.1, C87.2, C88.1, D1.1, D9.1, D14.2, IC4.2 (GND), IC12.7 (GND), IC13.3 (GND), J4.2, J12.1, R74.2, R77.2, R90.2, R119.2, R120.2, TP12.1, TP17.1, TP44.1, U1.2 (GND), U2.3 (AGND), U2.6 (MODE), U2.9 (PGND1), U2.11 (PGND2), U3.2 (GND), U5.2 (GND), U6.9 (PGND), U6.10 (PGND), U6.11 (PGND), U6.17 (PGND), U6.23 (AGND), U6.28 (AGND)
unnamed: C23.1, F1.1, L5.2, TP5.1, U1.4 (FB)
unnamed: C24.2, R45.1
unnamed: C28.2, R75.2
unnamed: C55.1, F2.2, L6.2, TP8.1, U5.4 (FB)
unnamed: C57.2, R89.1
unnamed: C61.2, R93.2, U6.20 (VOUT)
unnamed: F3.1, J4.1
unnamed: IC4.3 (EN), R92.1
unnamed: IC12.2 (1B), IC12.6 (~2Y), R16.2
unnamed: IC12.8 (~3Y), R130.2
unnamed: IC12.9 (3A), IC12.10 (3B), IC12.11 (~4Y)
unnamed: L5.1, U1.5 (SW)
unnamed: L6.1, U5.5 (SW)
unnamed: R39.1, U1.3 (EN)
unnamed: R52.1, U5.3 (EN)
unnamed: R70.1, U2.13 (RBOOT)
PWR_EN: IC13.4 (Y), R130.1
PWR_GOOD: R87.1, R96.2, TP40.1, U6.2 (PGOOD)
Q: D13.C, IC12.3 (~1Y), IC12.5 (2B), R36.2, R85.1
QDEL: C63.2, D13.A, IC12.12 (4A), IC12.13 (4B), IC13.2 (A), R85.2, R87.2
VDD_5V_DCDC: C84.1, R76.2, R96.1, U6.26 (VDD)
VDRV_5V_DCDC: C85.1, U6.16 (VDRV)
VIN: D14.1, F3.2, FB1.1, FB3.1, TP16.1
\~PWR_SET: C41.2, IC12.1 (1A), R84.1

Notes on the sheet:
Power sequencer
9...36 VDC
FAN 5V
3V3 DC/DC
Text
0.8V typ
R_FB_H = R_FB_L * (V_OUT - V_FB) / V_FB 10k * (5 - 0.8) / 0.8 = 52K5
Power Supply
Note: SIC477 can be substituted with SIC472. If so: R75, R77, R94, C28, C61, C82 are populated, R76, R93 are DNP
Note: Place close to the feedback resistors
52k3 -> 4.98V
3V3/3.5A
12A
Power input
Power save mode enabled, VDD, VDRVPre-reg on
5V/8A
#PWR_RST
5V DC/DC
3V3 FFC 1&2
System 1V8
52k5 -> 5.0V
1MHz
