TianmingLi/jetson-nano-baseboard/usb-debug.kicad_sch

## KiCad design usb-debug.kicad_sch (2023-06-30)

Schematic: usb-debug.kicad_sch

Parts:
C15, C29: C_47p_0402; 0402-cap; MPN C0402C470J5GACTU
C30, C33, C48, C50, C53, C54, C72, C90: C_100n_0402; 0402-cap; MPN 0402X104K6R3CT
C31: 100u; 1206; Voltage 6.3V; MPN C1206C107M9PACTU
C32: C_10u_0402; 0402-cap; MPN GRM155R60J106ME44D
C34: C_47u_0805; 0805-cap; MPN C0805C476M9PACTU
C35: C_10u_0603; 0603-cap; MPN GRM188R61A106KE69D
C62: C_4u7_0402; 0402-cap; MPN GRM155R61A475MEAAD
C66: C_1u_0402; 0402-cap; MPN C1005X6S1A105K050BC
C67: C_2u2_0402; 0402-cap; MPN C1005X5R1A225K050BC
D3, D5: PESD2USB5UV-TR; SOT-23s; MPN PESD2USB5UV-TR
D6, D7, D8: TPD4E05U06_PASS; MPN TPD4E05U06DQAR
D17: 1N4148WS; SOD-323; MPN 1N4148WS
IC1, IC3: NCP380LSNAJAAT1G; SOT-23-6; MPN NCP380LSNAJAAT1G
IC5: QFN-32; PartNumber FT232RQ
IC7: HD3SS3220; RNH0030A; MPN HD3SS3220RNHT
IC15: TPS7A0518PDBVT; SOT-23-5; MPN TPS7A0518PDBVT
J5, J9: JLC_USB-C-SMD_KH-TYPE-C-16P; PartSymbol 47346-0001
J11: 632723300011; WE_632723300011; MPN 632723300011
L2, L3, L7, L11: BLM18SG121TN1D; 0603; MPN BLM18SG121TN1D
LED1, LED2: LED0603; MPN KPT-1608SGC
R20, R41: R_22R_0402; 0402-res; MPN CRCW040222R0FKED
R42, R49, R56, R62, R63, R64, R65, R66, R68, R103, R104, R105, R106, R107, R108, R109, R110, R124, R125, R126, R127, R129, R136: R_0R_0402; 0402-res; MPN ERJ2GE0R00X
R43, R135: R_470R_0402; 0402-res; MPN CRCW0402470RFKED
R47, R102: R_100k_0402; 0402-res; MPN CRCW0402100KFKEDHP
R50, R54, R72, R131, R133, R134, R137, R138, R140, R141, R142, R143: R_10k_0402; 0402-res; MPN CRCW040210K0FKEDHP
R51: R_909k_0402; 0402-res; MPN ERJ2RKF9093X
R53, R67: R_200k_0402; 0402-res; MPN RC0402FR-07200KL
R55, R73: R_2k_0402; 0402-res; MPN CRCW04022K00FKED
T6, T7, T9: BSS138APW; SC70-3; MPN BSS138PW
TP18, TP19, TP21, TP32: TP-R-1.5; MPN N/A
U8: 74LVC1G07GV; SOT-753; MPN 74LVC1G07GV,125

Connections:
1V8_DBG: C66.2, IC5.1 (VCCIO), IC15.5 (VOUT)
1V8_SYS: R133.1
3V3_SYS: C33.1, IC7.8 (VCC33), R53.2
5V0_DBG: C67.2, C72.2, D17.C, IC5.19 (VCC), IC15.1 (VIN), IC15.3 (EN), L3.2
5V0_SYS: C32.1, C34.2, C90.2, D17.A, IC1.1 (IN), IC3.1 (IN), IC7.30 (VDD5), R42.1, R43.2, R47.2, R54.1, R55.1, R67.2, R102.2, R126.2, R134.2, R135.2, R136.1, U8.5 (VCC)
CC1: IC7.2 (CC1), R63.1, R66.2
CC2: IC7.1 (CC2), R64.1, R65.2
C_CC1: D5.2 (IO2), J11.A5 (CC1), R63.2, R64.2
C_CC2: D5.1 (IO1), J11.B5 (CC2), R65.1, R66.1
C_USBSS_RX1_N: D6.1 (CH1), J11.B10 (SSRXn1), R104.2
C_USBSS_RX1_P: D6.2 (CH2), J11.B11 (SSRXp1), R106.2
C_USBSS_RX2_N: D7.5 (CH4), J11.A10 (SSRXn2), R109.2
C_USBSS_RX2_P: D7.4 (CH3), J11.A11 (SSRXp2), R110.2
C_USBSS_RX6_N: IC7.10 (RXn), R108.2
C_USBSS_RX6_P: IC7.9 (RXp), R107.2
C_USBSS_TX1_N: C50.1, D6.5 (CH4), J11.A3 (SSTXn1)
C_USBSS_TX1_P: C48.1, D6.4 (CH3), J11.A2 (SSTXp1)
C_USBSS_TX2_N: C54.1, D7.1 (CH1), J11.B3 (SSTXn2)
C_USBSS_TX2_P: C53.1, D7.2 (CH2), J11.B2 (SSTXp2)
C_USBSS_TX6_N: IC7.7 (TXn), R105.2
C_USBSS_TX6_P: IC7.6 (TXp), R103.2
DBG_USB_D_N: C29.2, D3.1 (IO1), IC5.15 (USBDN), J9.A7 (D-), J9.B7 (D-)
DBG_USB_D_P: C15.2, D3.2 (IO2), IC5.14 (USBDP), J9.A6 (D+), J9.B6 (D+)
EN_MUX: IC7.12 (ENn_MUX), R56.2, R68.1
GEN0_SCL: R124.1
GEN0_SDA: R125.1
GND: C15.1, C29.1, C30.1, C31.1, C32.2, C33.2, C34.1, C35.1, C62.1, C66.1, C67.1, C72.1, C90.1, D3.3 (GND), D5.3 (GND), D6.3 (GND), D6.8 (GND), D7.3 (GND), D7.8 (GND), D8.3 (GND), D8.8 (GND), IC1.2 (GND), IC3.2 (GND), IC5.4 (GND), IC5.17 (GND), IC5.20 (GND), IC5.24 (AGND), IC5.26 (TEST), IC7.13 (GND), IC7.28 (GND), IC7.31 (GND), IC15.2 (GND), J5.A1 (GND), J5.A12 (GND), J5.B1 (GND), J5.B12 (GND), J9.A1 (GND), J9.A12 (GND), J9.B1 (GND), J9.B12 (GND), J11.A1 (GND), J11.A12 (GND), J11.B1 (GND), J11.B12 (GND), J11.Shell (Shield), L7.1, R50.2, R56.1, R62.1, R73.2, R127.1, R131.1, R137.1, R138.2, R140.2, R141.2, R142.2, R143.2, T6.2 (S), T7.2 (S), U8.3 (GND)
unnamed: C30.2, IC5.16 (3V3OUT)
unnamed: C31.2, IC3.6 (OUT), L2.1, R42.2
unnamed: IC1.5 (ILIM), R50.1
unnamed: IC1.6 (OUT), L11.1, R136.2
unnamed: IC3.3 (~EN), R49.2, R102.1, R137.2, T7.3 (D)
unnamed: IC3.4 (~FAULT), LED1.2 (K)
unnamed: IC3.5 (ILIM), R138.1
unnamed: IC5.2 (RXD), R41.1
unnamed: IC5.30 (TXD), R20.1
unnamed: IC7.3 (CURRENT_MODE), R54.2
unnamed: IC7.4 (PORT), R55.2
unnamed: IC7.5 (VBUS_DET), R51.1
unnamed: IC7.11 (DIR), R53.1
unnamed: IC7.29 (ENn_CC), R62.2
unnamed: J5.A5 (CC1), R140.1
unnamed: J5.B5 (CC2), R141.1
unnamed: J5.S1 (SHIELD), L7.2
unnamed: J9.A5 (CC1), R143.1
unnamed: J9.B5 (CC2), R142.1
unnamed: J11.B8 (SBU2), TP19.1
unnamed: LED1.1 (A), R43.1
unnamed: LED2.1 (A), R135.1
unnamed: R72.2, R73.1, T6.1 (G)
unnamed: R129.1, T6.3 (D), T9.2 (S)
OTG_USB_D_N: D8.1 (CH1), J5.A7 (D-), J5.B7 (D-)
OTG_USB_D_P: D8.2 (CH2), J5.A6 (D+), J5.B6 (D+)
OTG_USB_ID: D8.4 (CH3), IC1.3 (~EN), R134.1, T9.1 (G), U8.2 (A)
OTG_USB_VBUS: C62.2, J5.A4 (VBUS), J5.A9 (VBUS), J5.B4 (VBUS), J5.B9 (VBUS), L11.2, R72.1
SHIELD: J9.S1 (SHIELD)
UART1_RX: R20.2
UART1_TX: R41.2
USB1_D_N: J11.A7 (Dn1), J11.B7 (Dn2)
USB1_D_P: J11.A6 (Dp1), J11.B6 (Dp2)
USBC_ADDR: IC7.22 (ADDR), R126.1, R127.2, TP21.1
USBC_FAULT: IC7.24 (VCONN_FAULT_N), TP32.1
USBC_ID: IC7.27 (ID), R47.1, R49.1, R68.2, T7.1 (G), TP18.1
USBC_INTN: IC7.23 (INT_N/OUT3), R67.1
USBC_SCL: IC7.26 (SCL/OUT2), R125.2
USBC_SDA: IC7.25 (SDA/OUT1), R124.2
USBC_VBUS: C35.2, J11.A4 (VBUS), J11.A9 (VBUS), J11.B4 (VBUS), J11.B9 (VBUS), L2.2, R51.2, R131.2
USBSS_RX1_N: IC7.14 (RX1n), R104.1
USBSS_RX1_P: IC7.15 (RX1p), R106.1
USBSS_RX2_N: IC7.18 (RX2n), R109.1
USBSS_RX2_P: IC7.19 (RX2p), R110.1
USBSS_RX6_N: R108.1
USBSS_RX6_P: R107.1
USBSS_TX1_N: C50.2, IC7.17 (TX1p)
USBSS_TX1_P: C48.2, IC7.16 (TX1n)
USBSS_TX2_N: C54.2, IC7.21 (TX2p)
USBSS_TX2_P: C53.2, IC7.20 (TX2n)
USBSS_TX6_N: R105.1
USBSS_TX6_P: R103.1
USB_DBG_VBUS: J9.A4 (VBUS), J9.A9 (VBUS), J9.B4 (VBUS), J9.B9 (VBUS), L3.1
~OTG_USB_FAULT: IC1.4 (~FAULT), LED2.2 (K)
~OTG_USB_ID_DET: R133.2, U8.4 (Y)
~OTG_USB_VBUS_DET: R129.2, T9.3 (D)

Notes on the sheet:
LOAD SW
HIGH
VBUS_DET
DISC HOST DEVICE
STATE
LOW HIGH HIGH
Current limit set to 2.1A
OTG/Flash USB
USB
Text
DEVICE
NOTE: Mount for EN HIGH load switch DNP for EN LOW
USB_PW
VBUS
Debug USB connector
USB-C Connector
OTG TRUTH TABLE
ROLE
USB-C Load Switch
ID/VBUS DET signals
Debug UART
DIS
NOTE: Mount for EN LOW load switch DNP for EN HIGH
HIGH LOW HIGH
ID_DET
STATE
Both DNP - GPIO Mode HIGH - I2C Mode 0x67 LOW - I2C Mode 0x47
HOST
LOW
HIGH-Z HIGH-Z LOW
USB-C Multiplexer
USBC_ID
